Maxemmm/Projet-Long-n-2/images/3D/back-bottom-right.png

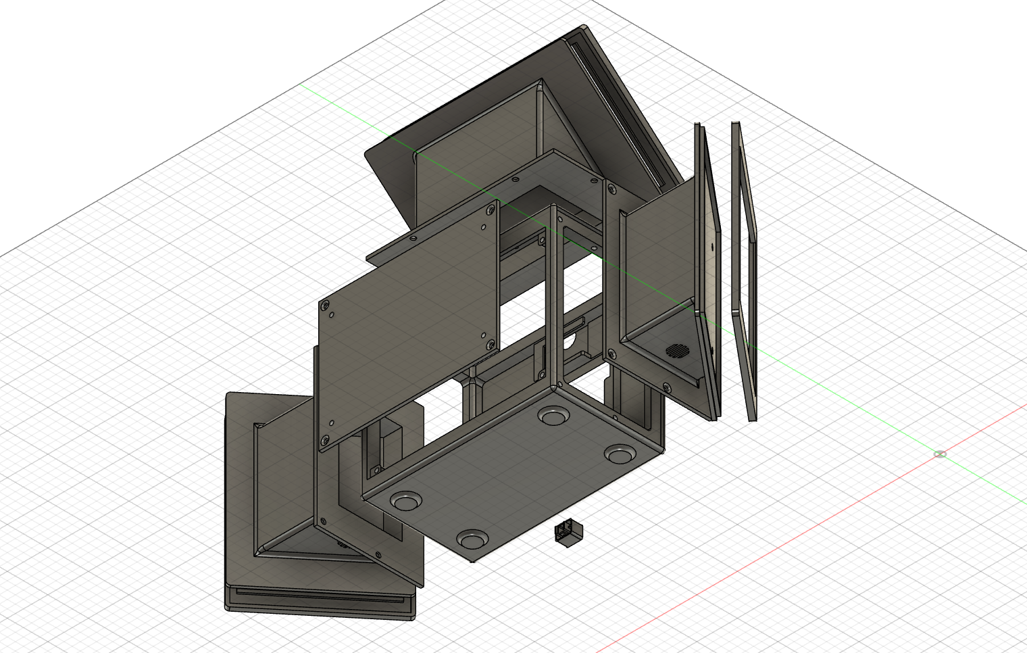
images/3D/back-bottom-right.png
