Maxemmm/Projet-Long-n-2/images/3D/back-upper-left.png

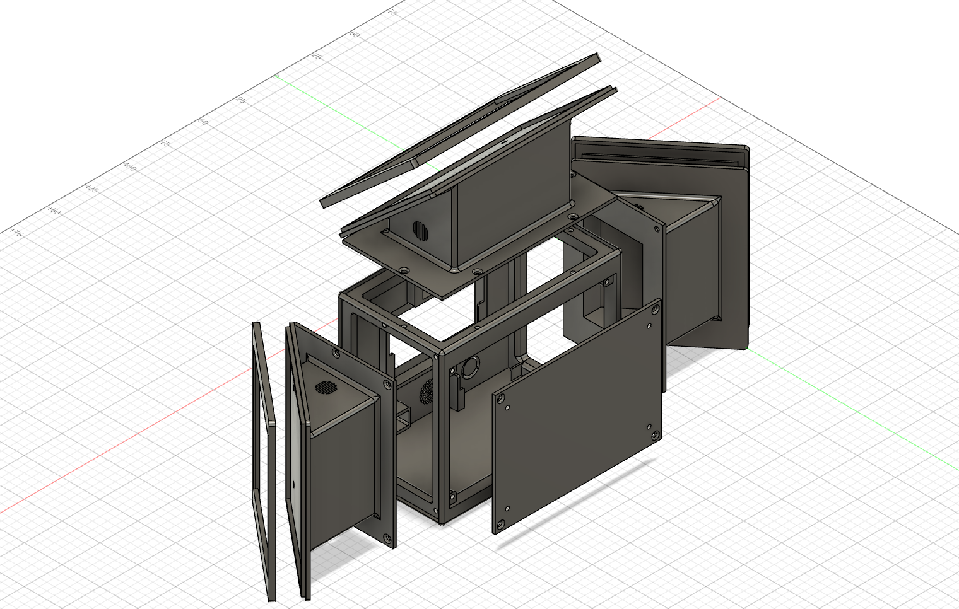
images/3D/back-upper-left.png
