Maxemmm/Projet-Long-n-2/images/3D/stock/back.png

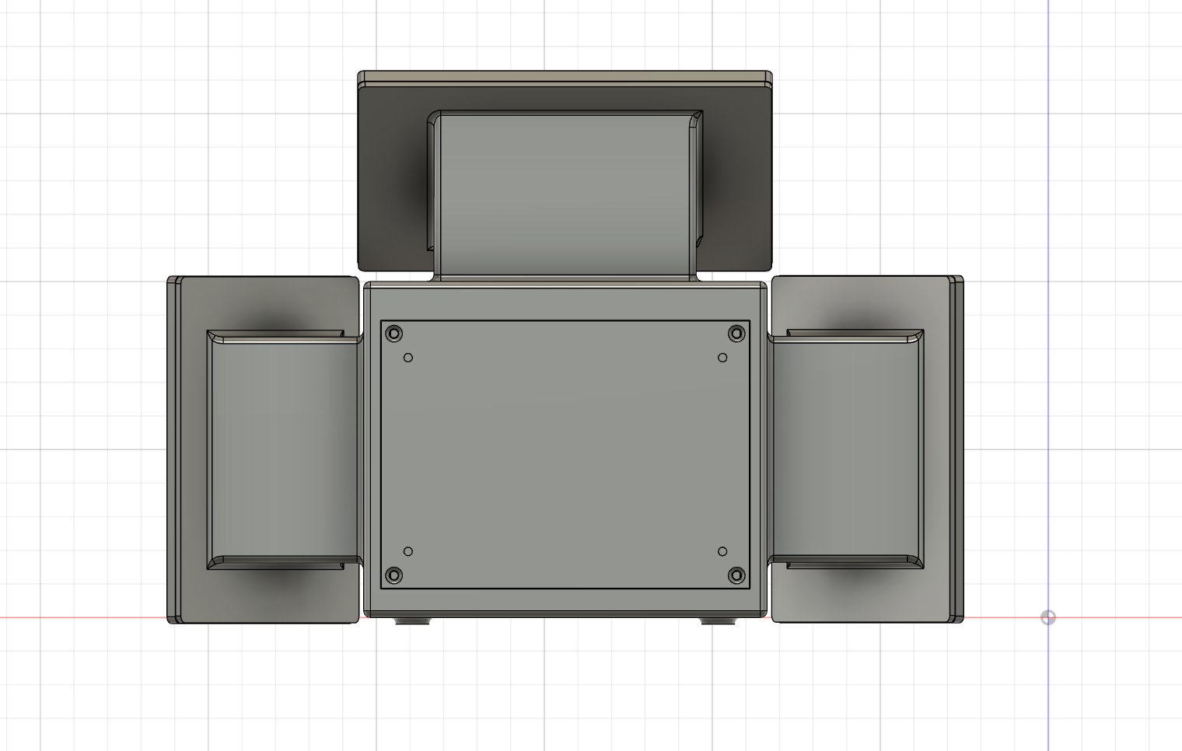
images/3D/stock/back.png
