Maxemmm/Projet-Long-n-2/images/HMI/ubidots.png

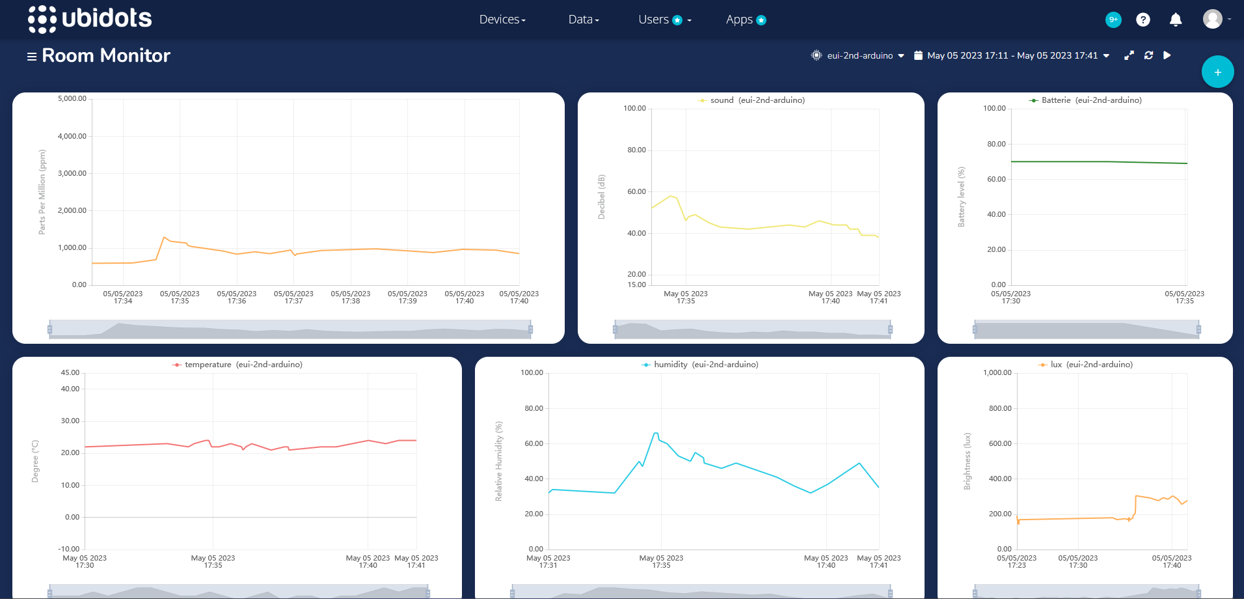
images/HMI/ubidots.png
